sergey12malyshev/MIDItesla/images/1677234725897.jpg

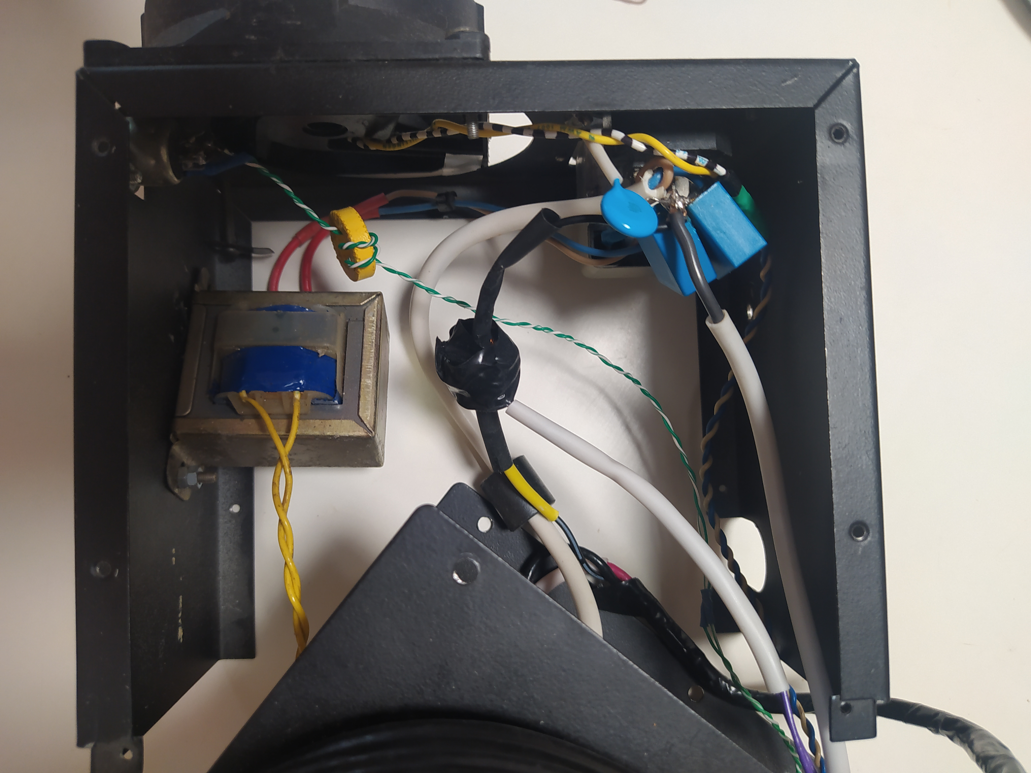
images/1677234725897.jpg
