sergey12malyshev/MIDItesla/images/1677234725920.jpg

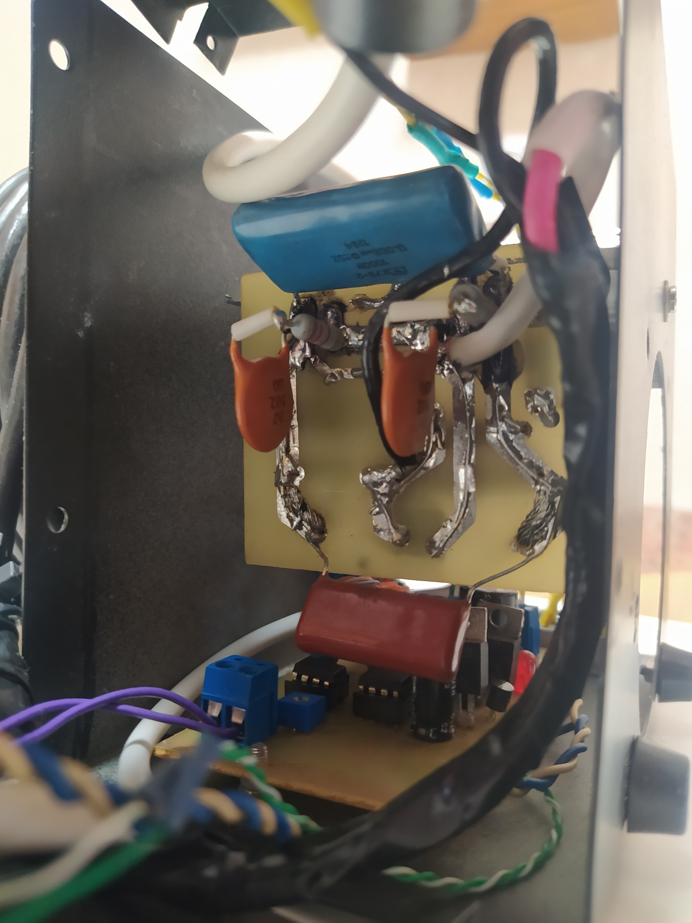
images/1677234725920.jpg
