sergey12malyshev/MIDItesla/images/1677241838365.jpg

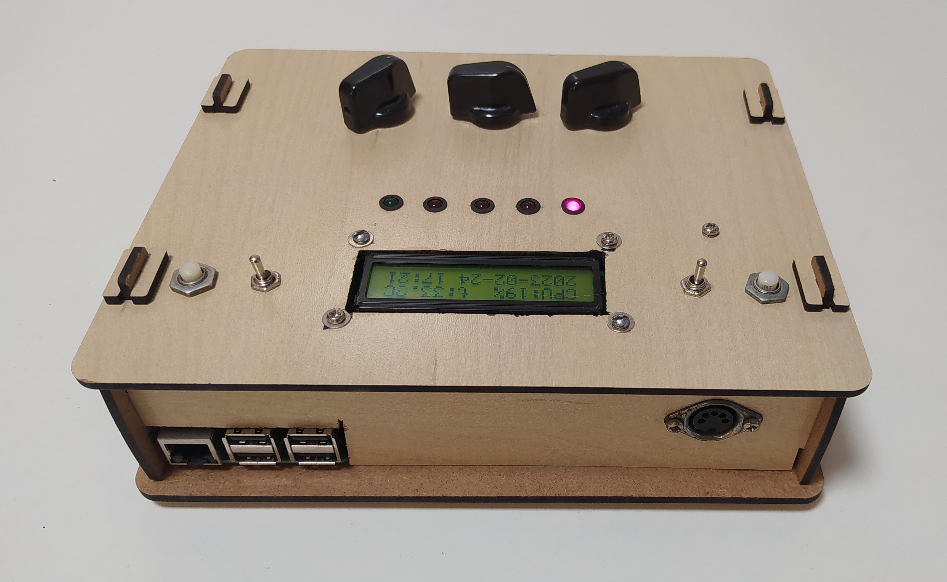
images/1677241838365.jpg
