sergey12malyshev/MIDItesla/images/1677241838375.jpg

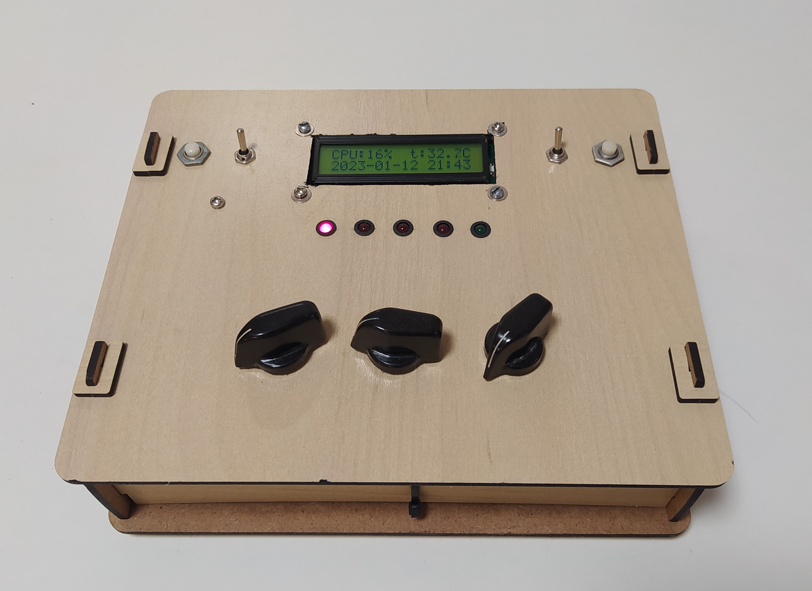
images/1677241838375.jpg
