sergey12malyshev/MIDItesla/images/1677242053874.jpg

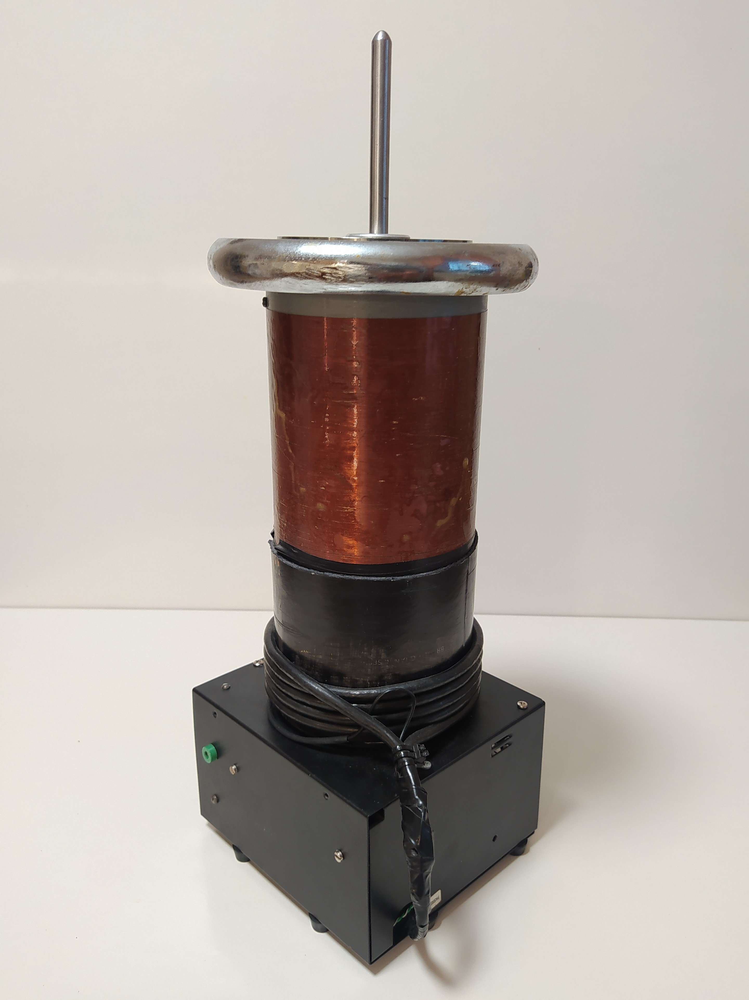
images/1677242053874.jpg
