sergey12malyshev/MIDItesla/images/1677242053886.jpg

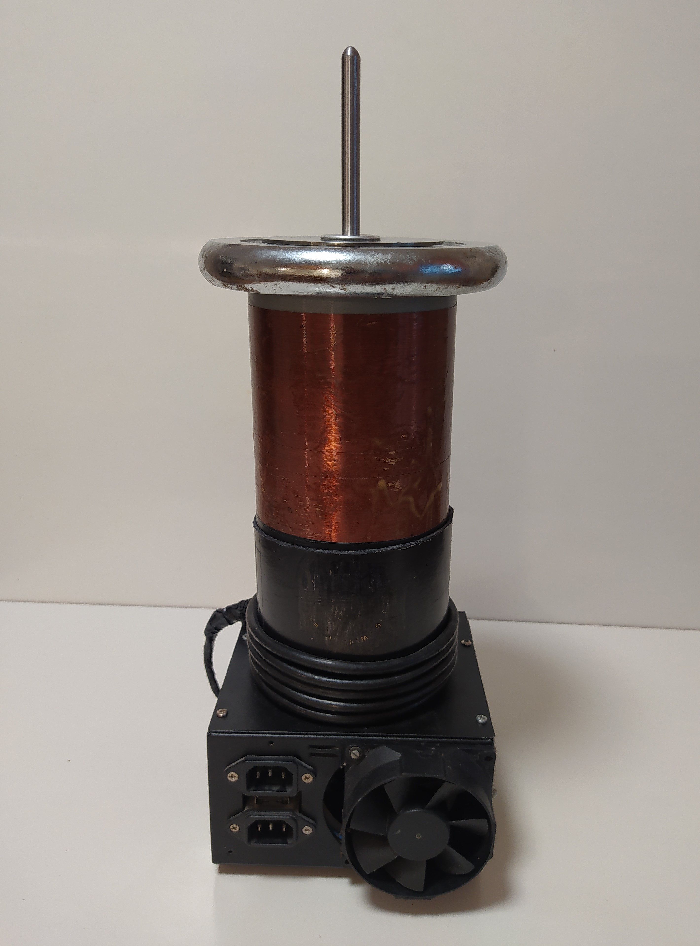
images/1677242053886.jpg
