sergey12malyshev/MIDItesla/images/1677242143809.jpg

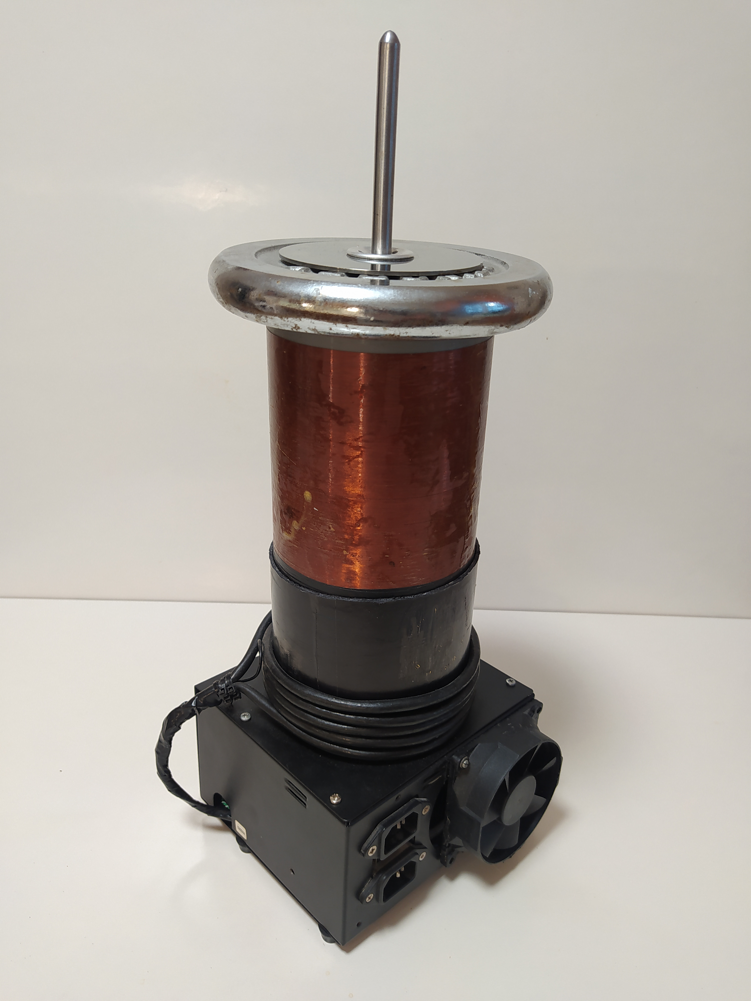
images/1677242143809.jpg
