sergey12malyshev/MIDItesla/images/1677244392221.jpg

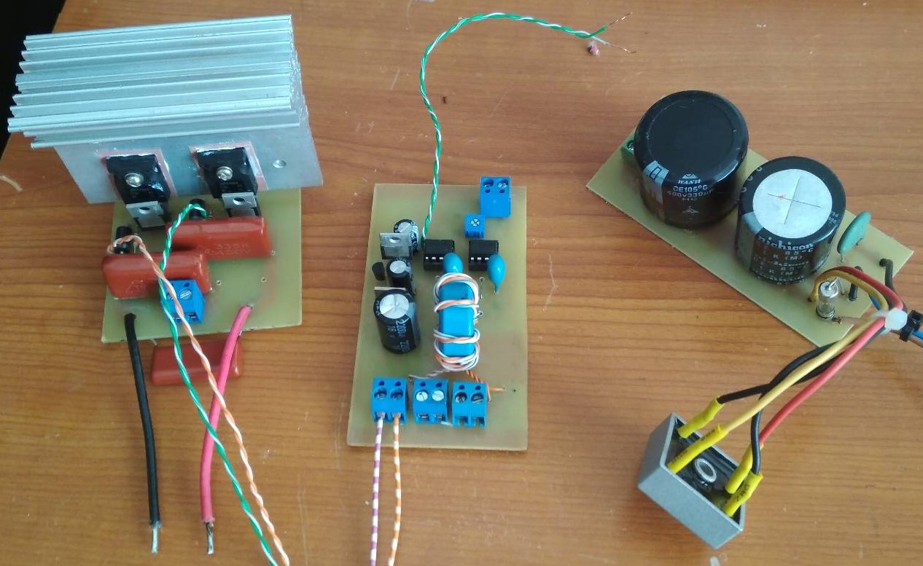
images/1677244392221.jpg
