sergey12malyshev/MIDItesla/schemes/1677514975394.jpg

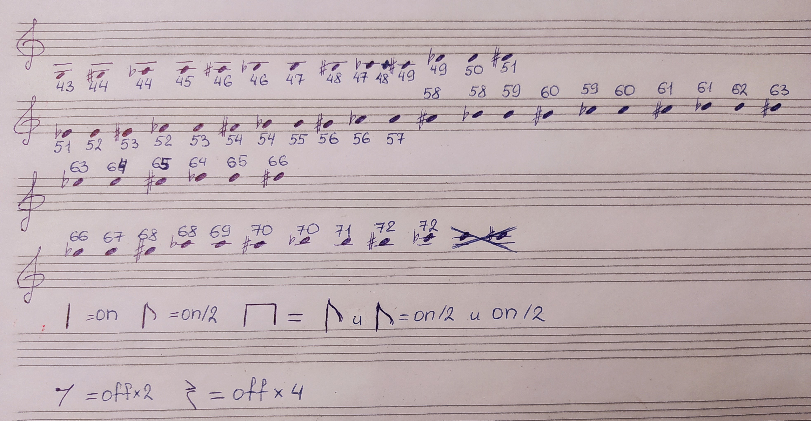
schemes/1677514975394.jpg
