sergey12malyshev/MIDItesla/schemes/b_pianokafe_oliver_adams_mortal_kombat_theme.jpg

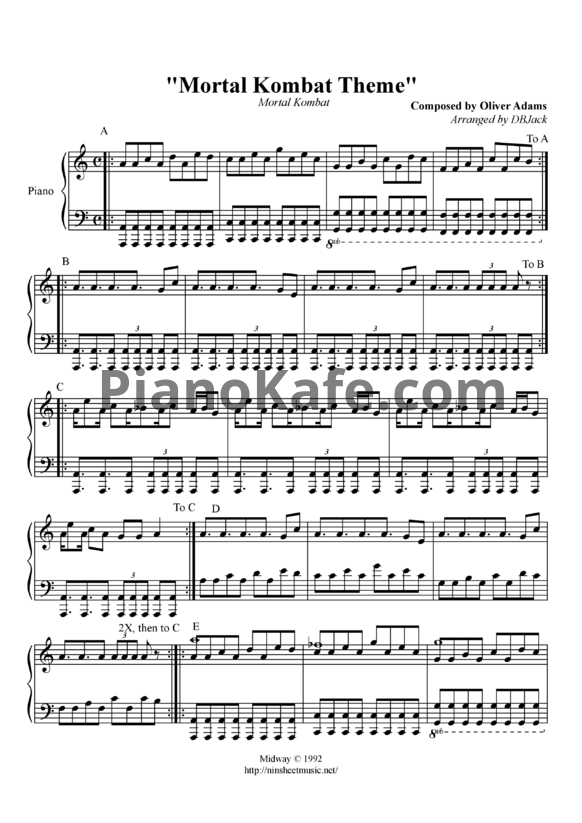
schemes/b_pianokafe_oliver_adams_mortal_kombat_theme.jpg
