sergey12malyshev/MIDItesla/schemes/Cхема_структурная.BMP

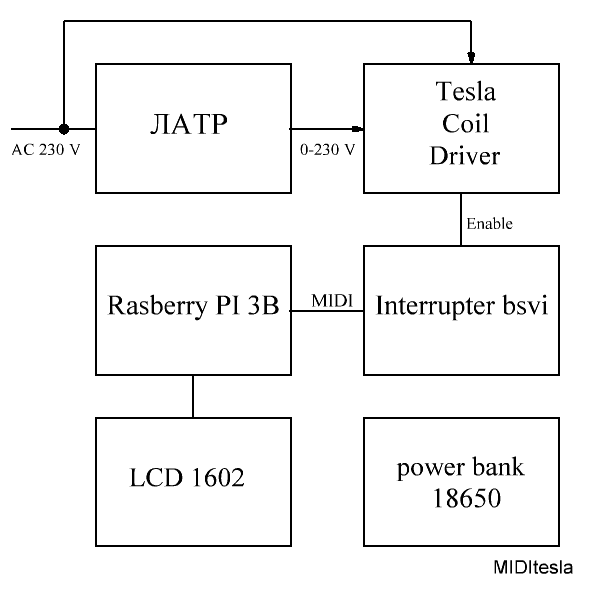
schemes/Cхема_структурная.BMP
